NCAR/iotwx-manual/build/stl/atmos/uv_cap.stl

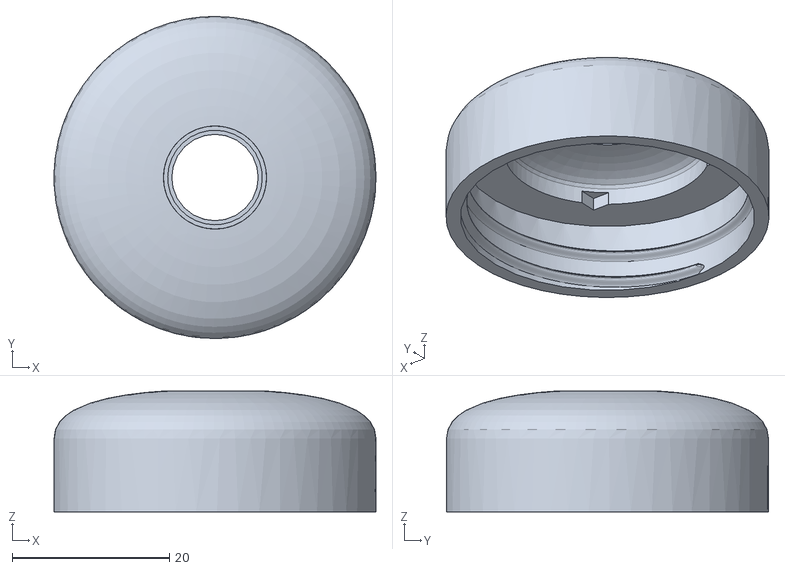
[picture p24: CAD file, 2020-11-18]
build/stl/atmos/uv_cap.stl
41.0 x 41.0 x 15.4
