NCAR/iotwx-manual/build/stl/hydro/hyd_funnel.stl

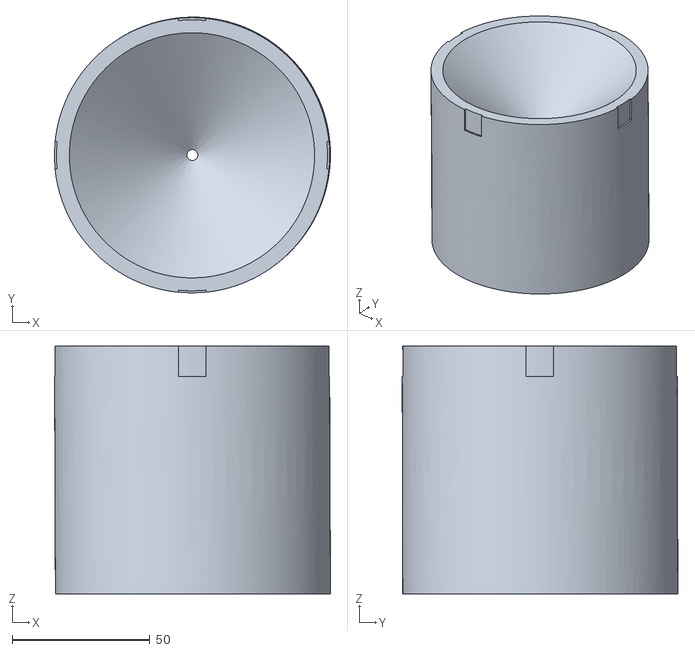
[picture p25: CAD file, 2020-11-18]
build/stl/hydro/hyd_funnel.stl
100.2 x 100.1 x 90.0
