NCAR/iotwx-manual/build/stl/aero/aero_wnvn_clips_3.stl

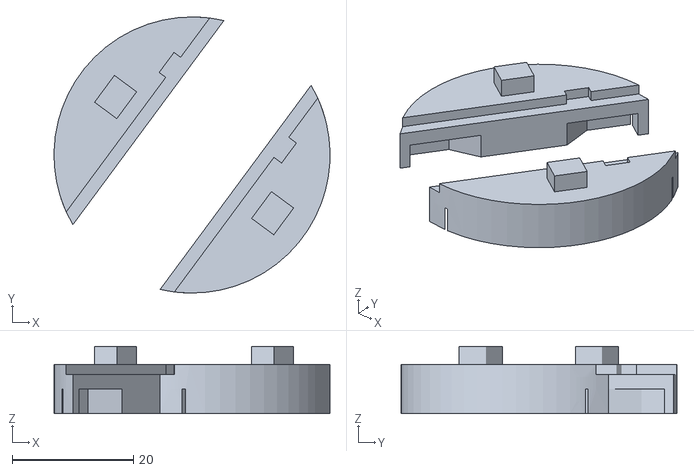
[picture p27: CAD file, 2020-11-18]
build/stl/aero/aero_wnvn_clips_3.stl
45.5 x 45.5 x 11.1
