NCAR/iotwx-manual/build/stl/atmos/rs_single_leaf.stl

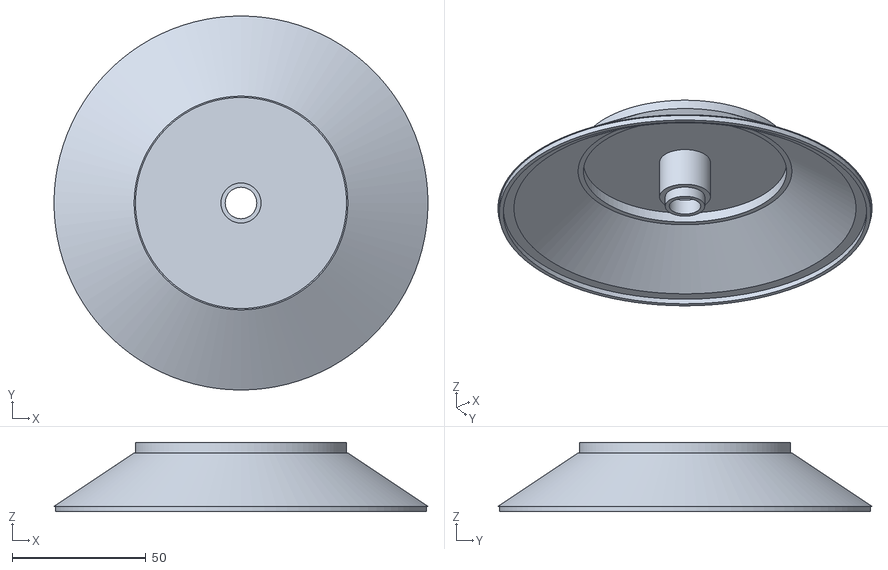
[picture p28: CAD file, 2020-11-18]
build/stl/atmos/rs_single_leaf.stl
140.0 x 140.0 x 25.9
