NCAR/iotwx-manual/build/stl/hydro/swvl_balljoint_bar.stl

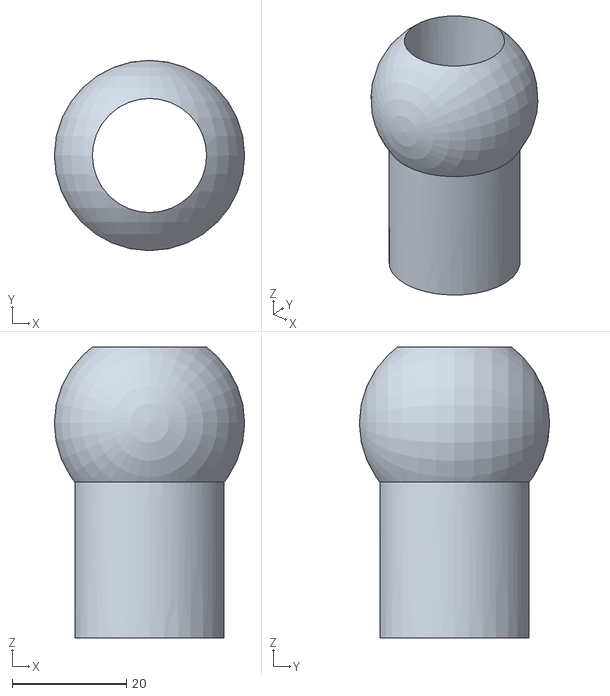
[picture p29: CAD file, 2020-11-18]
build/stl/hydro/swvl_balljoint_bar.stl
33.3 x 33.3 x 50.9
