NCAR/iotwx-manual/build/stl/pvc/pvc_tripod_base.stl

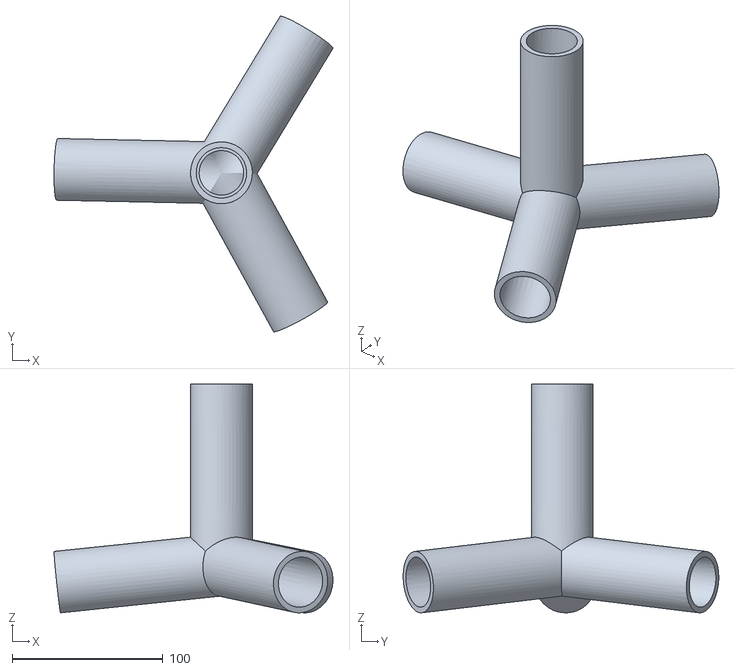
[picture p30: CAD file, 2020-11-18]
build/stl/pvc/pvc_tripod_base.stl
185.1 x 209.5 x 151.8
