NCAR/iotwx-manual/build/stl/aero/aero_wnvn_plate_3.stl

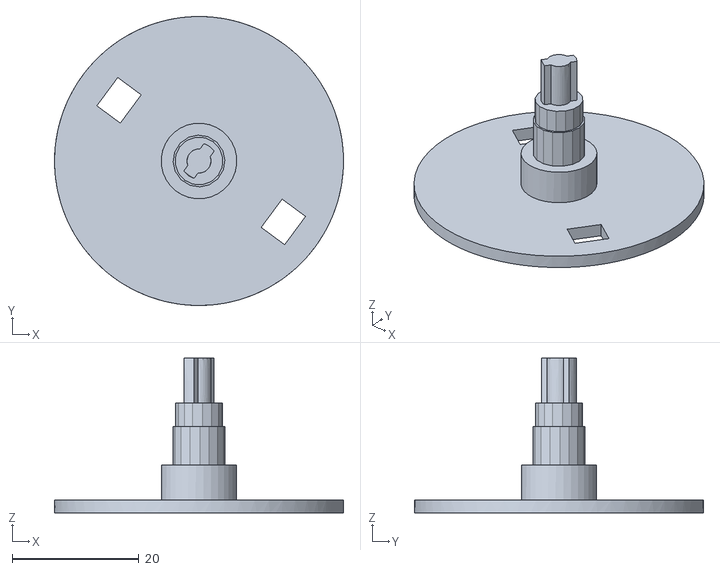
[picture p31: CAD file, 2020-11-18]
build/stl/aero/aero_wnvn_plate_3.stl
45.5 x 45.5 x 24.4
