NCAR/iotwx-manual/build/stl/atmos/rs_shaft.stl

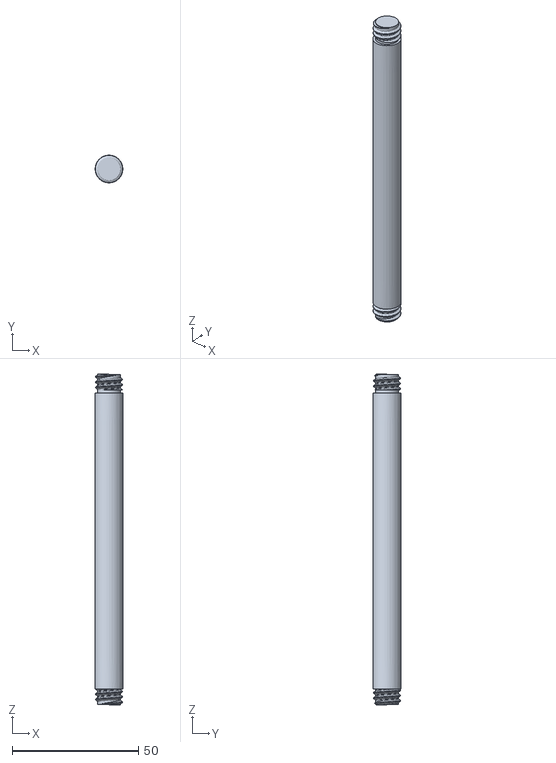
[picture p32: CAD file, 2020-11-18]
build/stl/atmos/rs_shaft.stl
11.0 x 11.0 x 131.2
