NCAR/iotwx-manual/build/stl/hydro/swvl_innerlock.stl

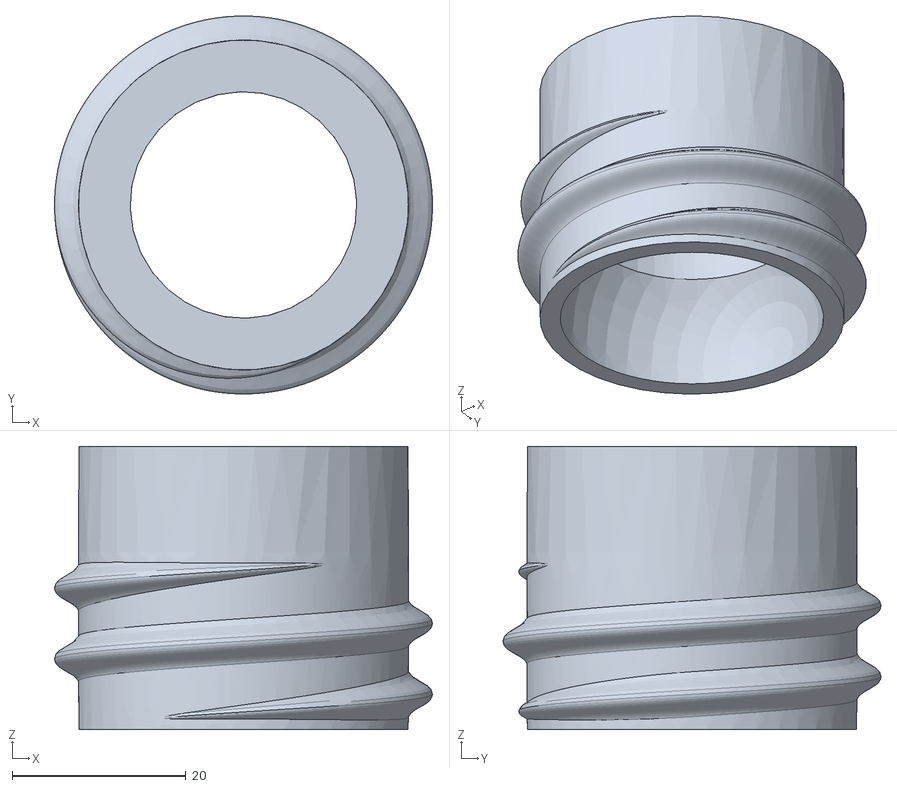
[picture p33: CAD file, 2020-11-18]
build/stl/hydro/swvl_innerlock.stl
43.5 x 43.5 x 32.6
