NCAR/iotwx-manual/build/stl/aero/aero_wnvn_coupler_3.stl

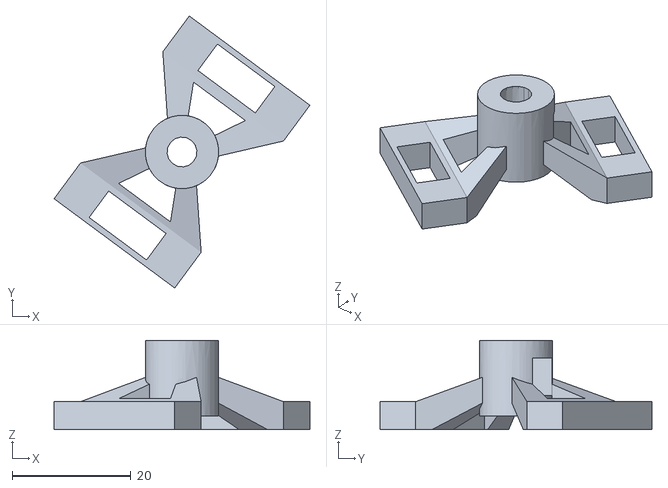
[picture p34: CAD file, 2020-11-18]
build/stl/aero/aero_wnvn_coupler_3.stl
43.1 x 45.8 x 15.0
