NCAR/iotwx-manual/build/stl/hydro/hyd_fulcrum.stl

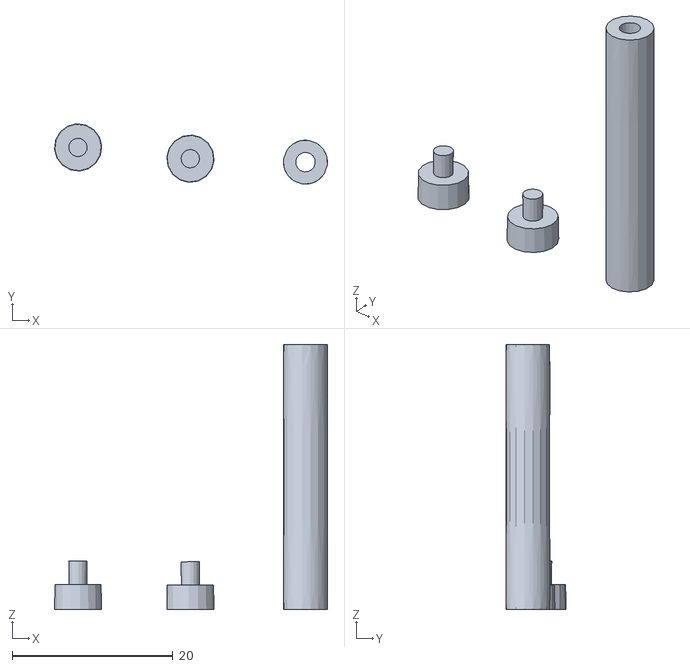
[picture p35: CAD file, 2020-11-18]
build/stl/hydro/hyd_fulcrum.stl
34.0 x 7.52 x 33.1
