NCAR/iotwx-manual/build/stl/atmos/rs_base.stl

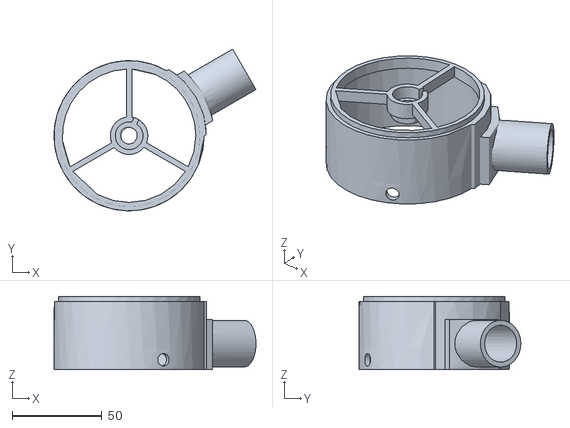
[picture p37: CAD file, 2020-11-18]
build/stl/atmos/rs_base.stl
112.8 x 90.3 x 41.0
