NCAR/iotwx-manual/build/stl/hydro/hyd_rain_guage.stl

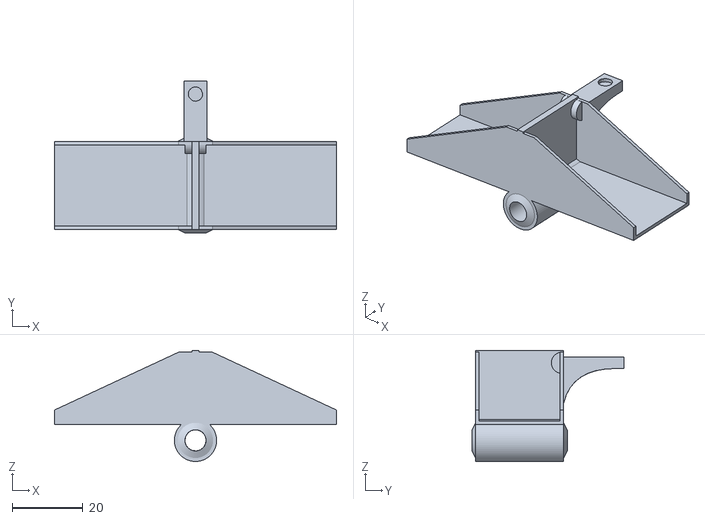
[picture p38: CAD file, 2020-11-18]
build/stl/hydro/hyd_rain_guage.stl
80.0 x 43.1 x 31.5
