NCAR/iotwx-manual/build/stl/pvc/pvc_tjoint.stl

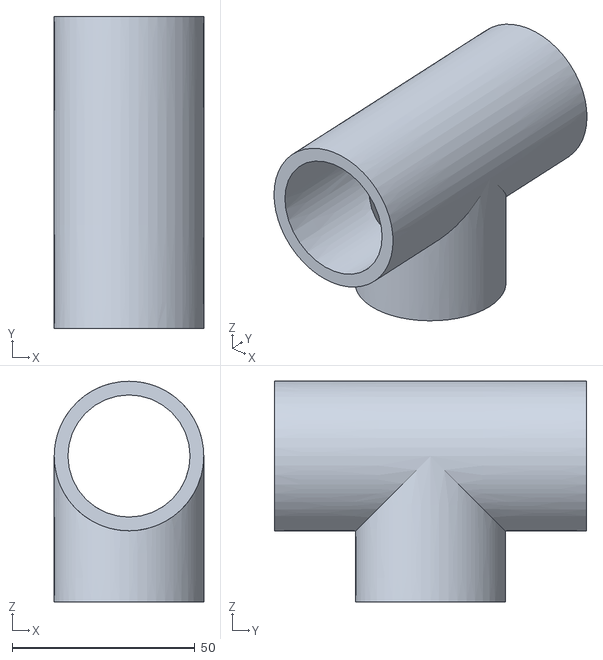
[picture p39: CAD file, 2020-11-18]
build/stl/pvc/pvc_tjoint.stl
40.9 x 85.3 x 60.3
