NCAR/iotwx-manual/build/stl/atmos/rs_base_plate.stl

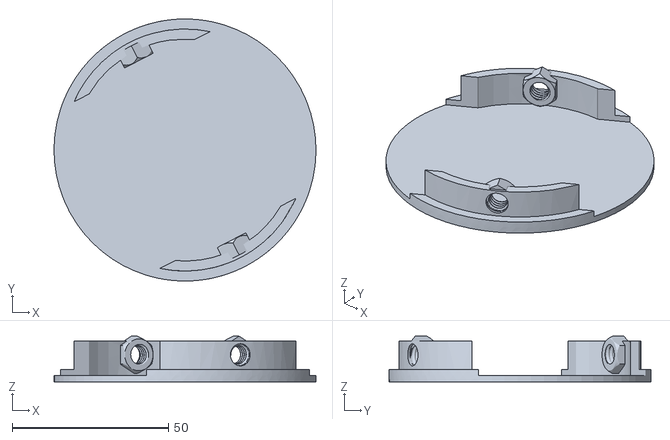
[picture p40: CAD file, 2020-11-18]
build/stl/atmos/rs_base_plate.stl
83.9 x 83.9 x 14.6
