NCAR/iotwx-manual/build/stl/atmos/rs_clip.stl

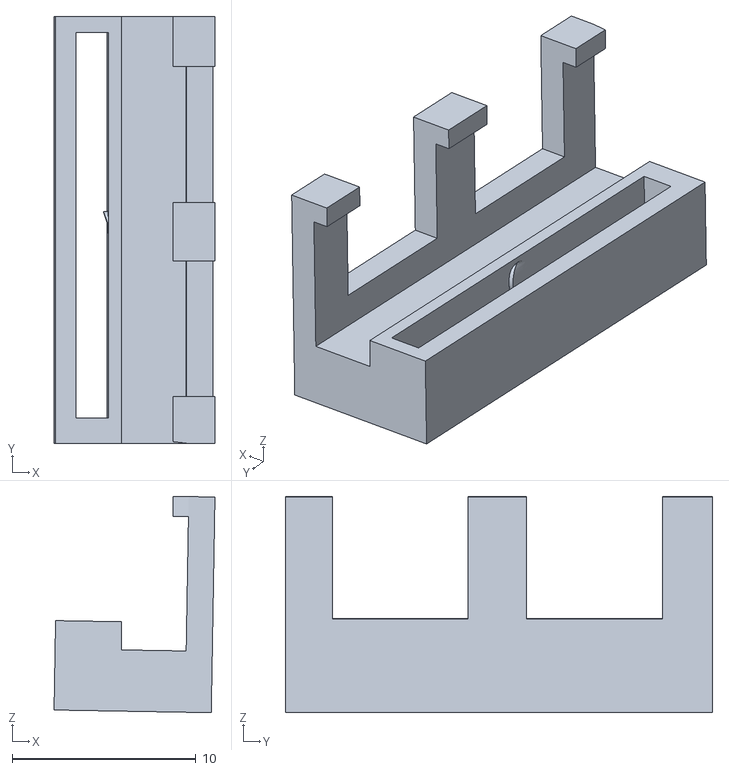
[picture p41: CAD file, 2020-11-18]
build/stl/atmos/rs_clip.stl
8.76 x 23.3 x 11.8
