NCAR/iotwx-manual/build/stl/atmos/rs_fasteners.stl

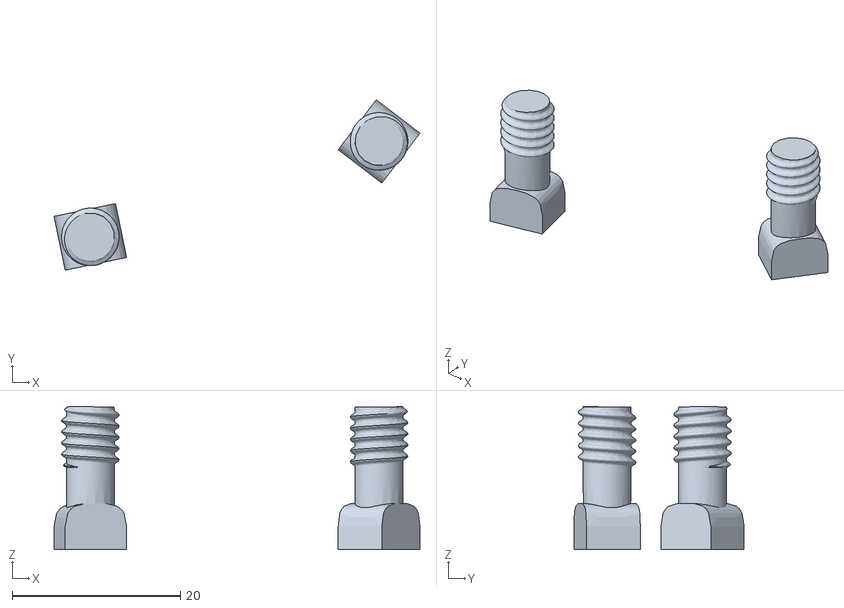
[picture p43: CAD file, 2020-11-18]
build/stl/atmos/rs_fasteners.stl
43.6 x 20.3 x 17.1
