NCAR/iotwx-manual/build/stl/pvc/pvc_en_cap.stl

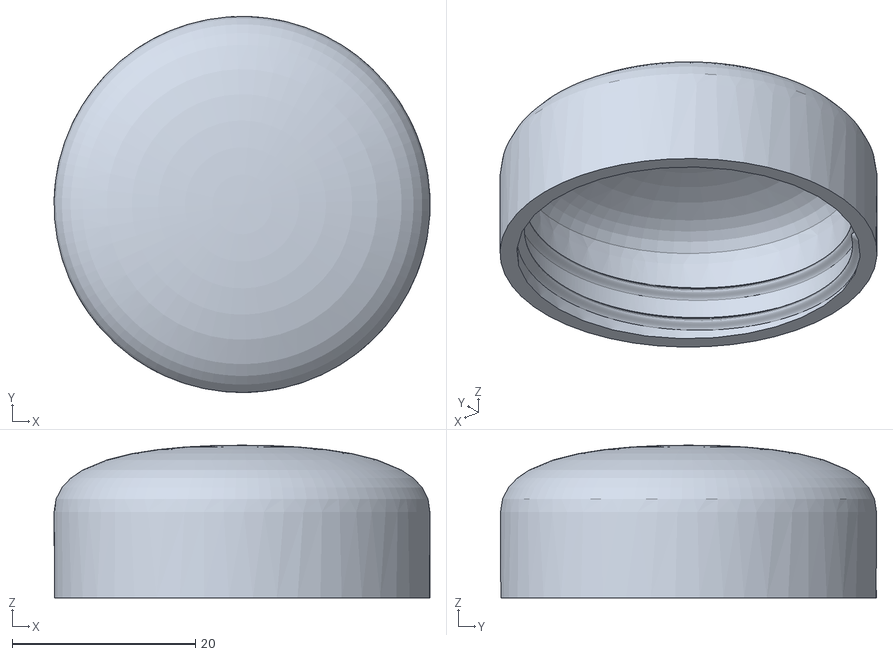
[picture p44: CAD file, 2020-11-18]
build/stl/pvc/pvc_en_cap.stl
41.0 x 41.0 x 16.6
