NCAR/iotwx-manual/build/stl/atmos/uv_tube.stl

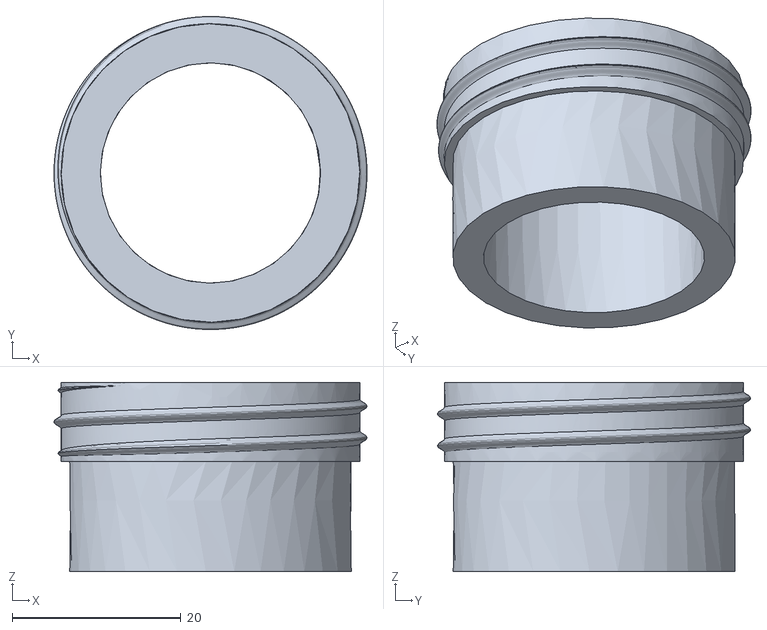
[picture p45: CAD file, 2020-11-18]
build/stl/atmos/uv_tube.stl
37.1 x 37.1 x 22.4
